Beenana02/Krill-Kam/GUIimages/exitScreen.png

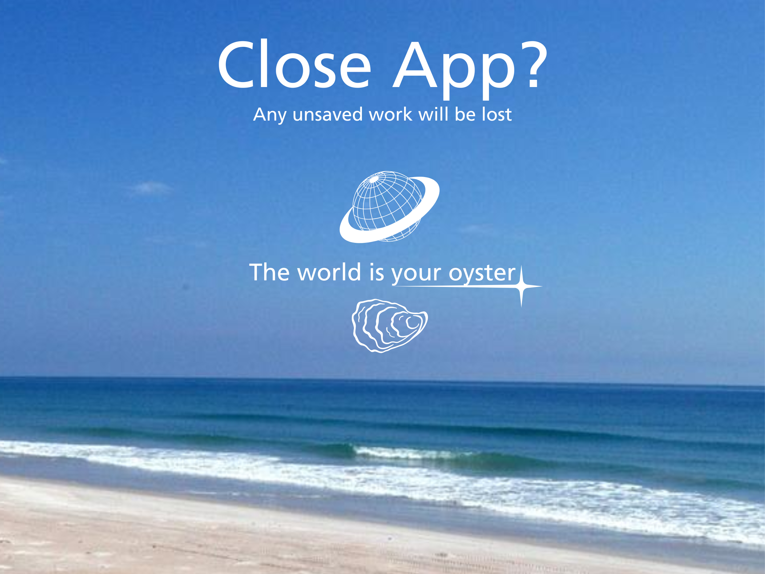
GUIimages/exitScreen.png
