Beenana02/Krill-Kam/Case/V2/BatteryHolder.stl

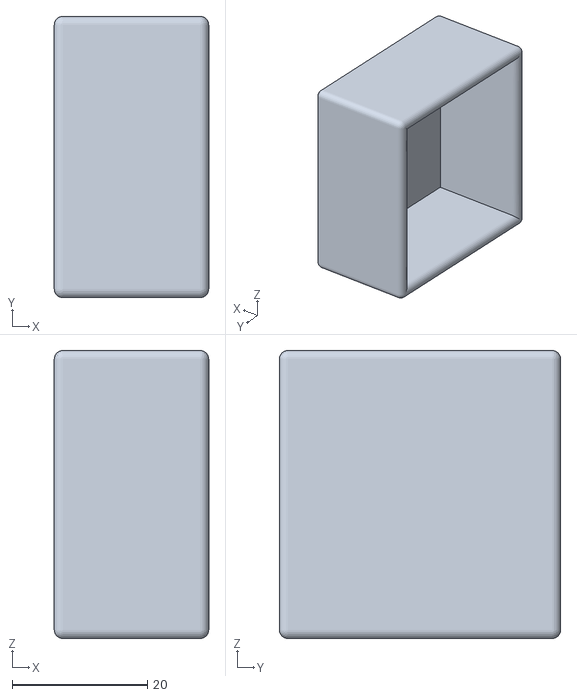
[picture p21: CAD file, 2025-06-05, an earlier design]
Case/V2/BatteryHolder.stl
22.9 x 41.6 x 42.6
