Beenana02/Krill-Kam/Case/V2/InnerPanel.stl

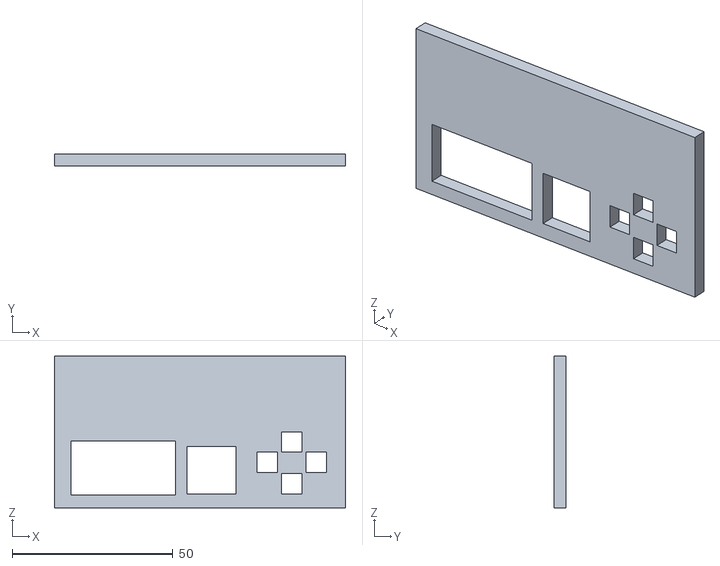
[picture p22: CAD file, 2025-06-05, an earlier design]
Case/V2/InnerPanel.stl
90.4 x 3.81 x 47.1
